Jojotheamazing/esp32-console/SdCard/Assets/UIImages/MainMenu/control.bmp

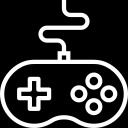
SdCard/Assets/UIImages/MainMenu/control.bmp
