Jojotheamazing/esp32-console/SdCard/Assets/UIImages/MainMenu/games.bmp

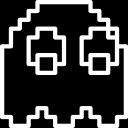
SdCard/Assets/UIImages/MainMenu/games.bmp
