Jojotheamazing/esp32-console/SdCard/music/DummyPlaylist2/cover.jpg

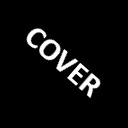
SdCard/music/DummyPlaylist2/cover.jpg
