Jojotheamazing/esp32-console/CAD/SecondaryColor/CompleteShell - ValinorStar1.step

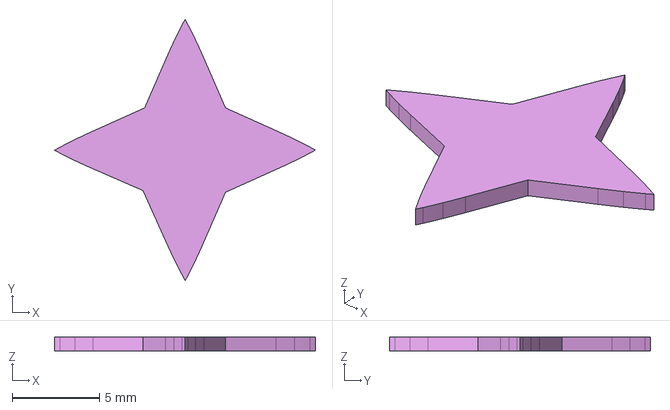
[picture p24: CAD file, 2026-09-23]
CAD/SecondaryColor/CompleteShell - ValinorStar1.step
14.9 x 15.0 x 0.8 mm
