Jojotheamazing/esp32-console/CAD/SecondaryColor/CompleteShell - BatteryCoverR.step

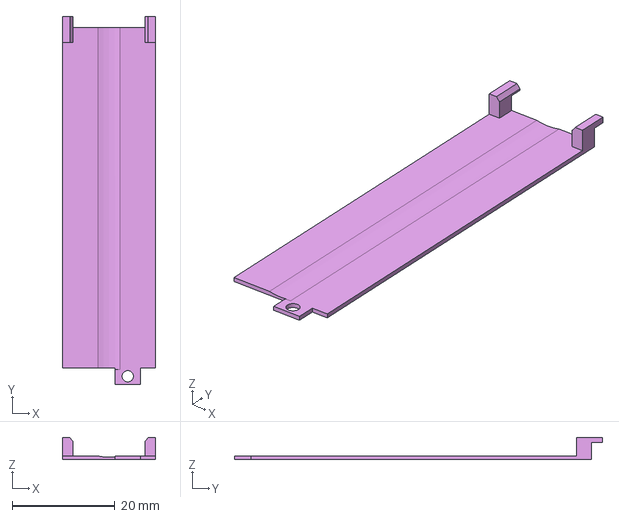
[picture p25: CAD file, 2026-09-23]
CAD/SecondaryColor/CompleteShell - BatteryCoverR.step
18.1 x 71.7 x 4.30 mm
