Jojotheamazing/esp32-console/CAD/SecondaryColor/CompleteShell - HackclubFlag.step

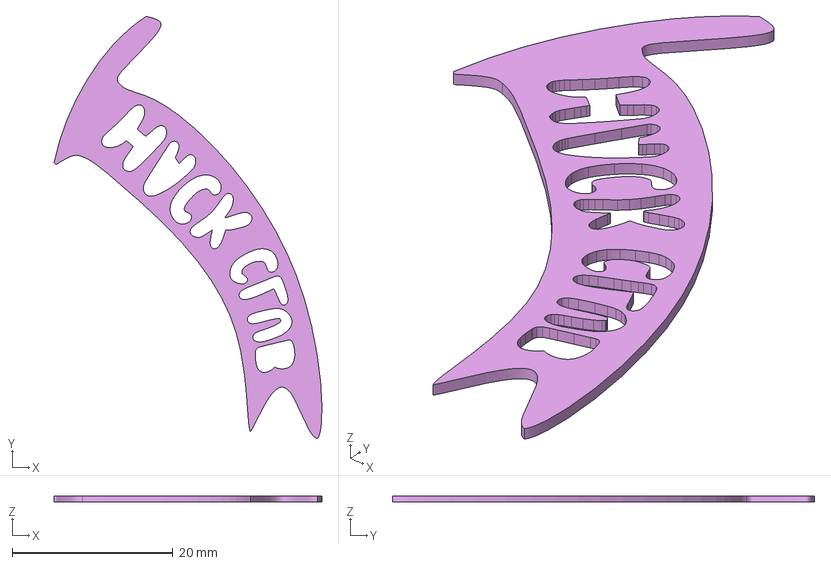
[picture p26: CAD file, 2026-09-23]
CAD/SecondaryColor/CompleteShell - HackclubFlag.step
33.4 x 52.6 x 0.8 mm
