Jojotheamazing/esp32-console/CAD/SecondaryColor/CompleteShell - ValinorStar3.step

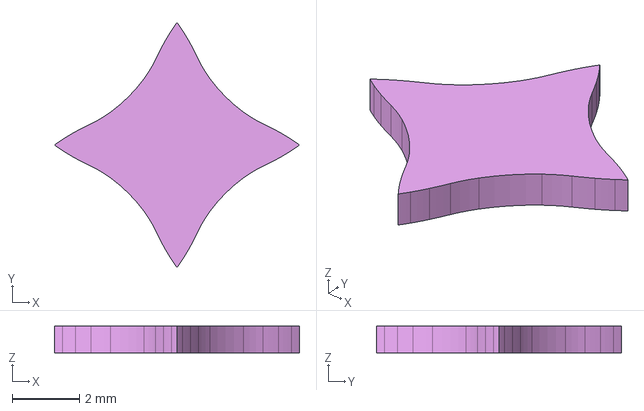
[picture p27: CAD file, 2026-09-23]
CAD/SecondaryColor/CompleteShell - ValinorStar3.step
7.31 x 7.31 x 0.8 mm
