Jojotheamazing/esp32-console/CAD/SecondaryColor/CompleteShell - GitLogo.step

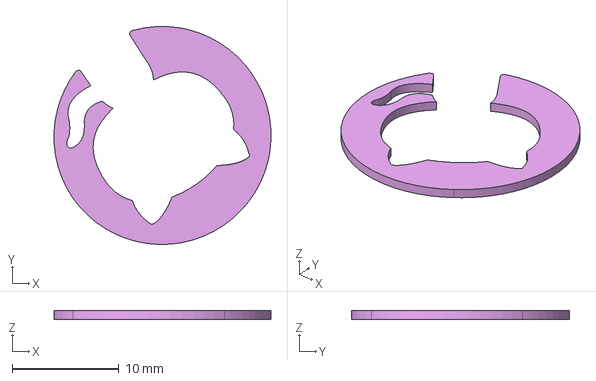
[picture p28: CAD file, 2026-09-23]
CAD/SecondaryColor/CompleteShell - GitLogo.step
20.3 x 20.4 x 0.8 mm
