Jojotheamazing/esp32-console/CAD/SecondaryColor/CompleteShell - ForgeLogo.step

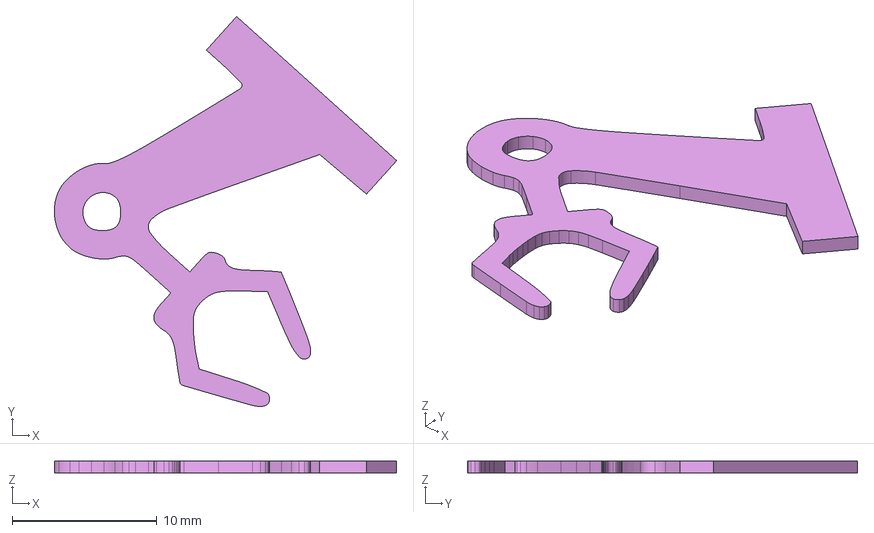
[picture p29: CAD file, 2026-09-23]
CAD/SecondaryColor/CompleteShell - ForgeLogo.step
23.6 x 26.9 x 0.8 mm
