Jojotheamazing/esp32-console/CAD/SecondaryColor/CompleteShell - ForgeO1.step

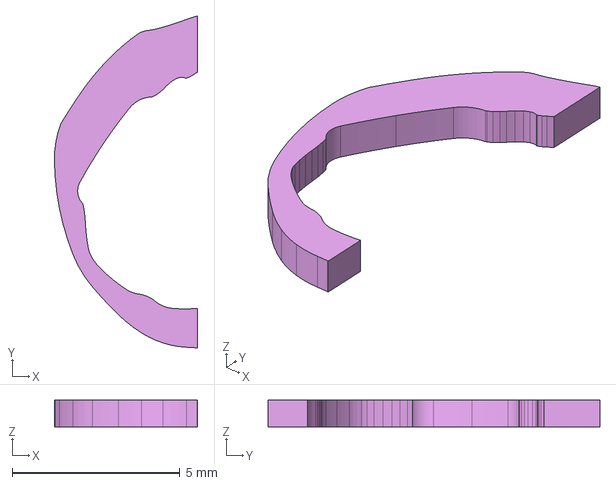
[picture p30: CAD file, 2026-09-23]
CAD/SecondaryColor/CompleteShell - ForgeO1.step
4.26 x 9.88 x 0.8 mm
