Jojotheamazing/esp32-console/CAD/MainColor/S_BUTTONS - Part 15.step

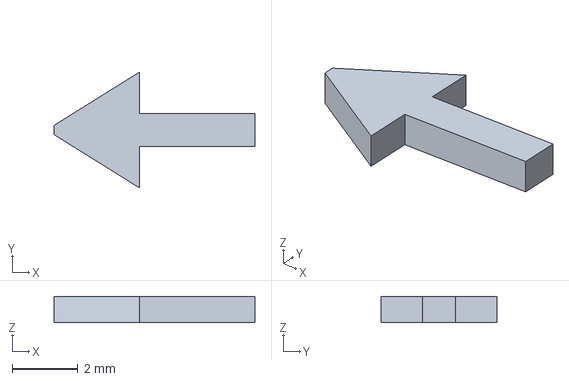
[picture p31: CAD file, 2026-09-23]
CAD/MainColor/S_BUTTONS - Part 15.step
6.10 x 3.52 x 0.8 mm
