Jojotheamazing/esp32-console/CAD/SecondaryColor/M_BUTTONS - StartButton.step

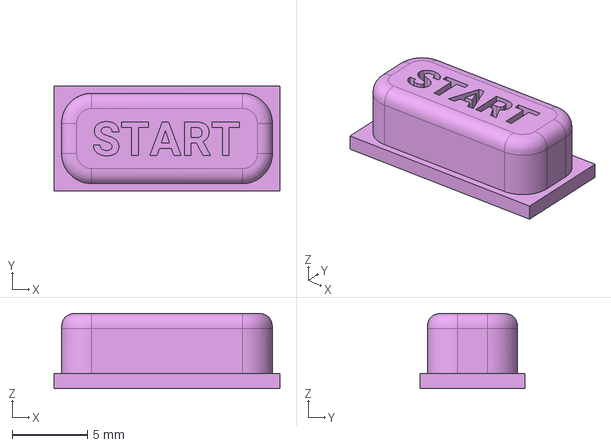
[picture p32: CAD file, 2026-09-23]
CAD/SecondaryColor/M_BUTTONS - StartButton.step
15.0 x 7.00 x 5.00 mm
