Jojotheamazing/esp32-console/CAD/MainColor/S_BUTTONS - Part 9.step

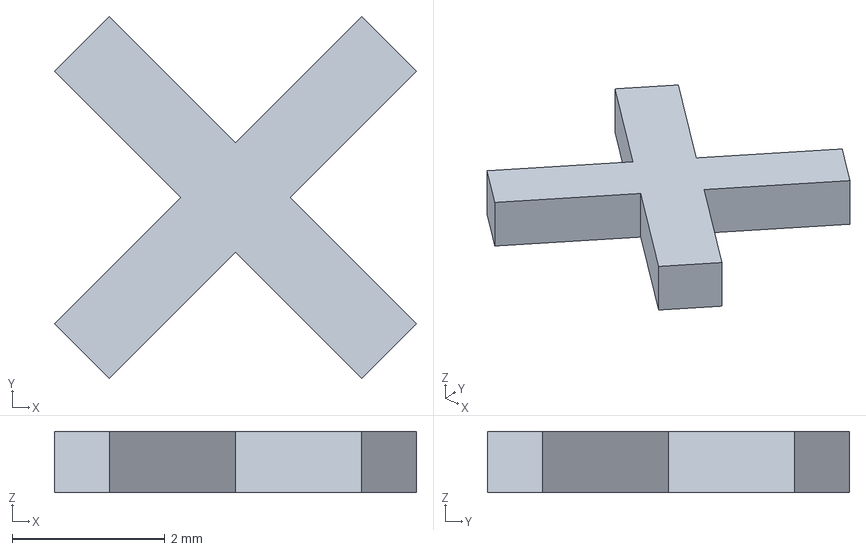
[picture p33: CAD file, 2026-09-23]
CAD/MainColor/S_BUTTONS - Part 9.step
4.74 x 4.74 x 0.8 mm
