Jojotheamazing/esp32-console/CAD/SecondaryColor/S_TOP - Volume.step

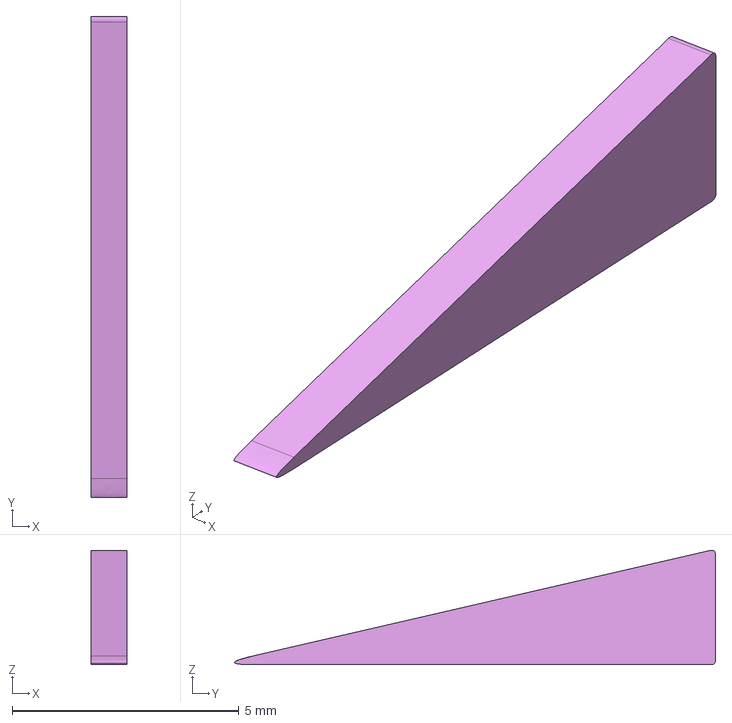
[picture p34: CAD file, 2026-09-23]
CAD/SecondaryColor/S_TOP - Volume.step
0.8 x 10.6 x 2.53 mm
