Jojotheamazing/esp32-console/CAD/SecondaryColor/M_BUTTONS - PowerButton.step

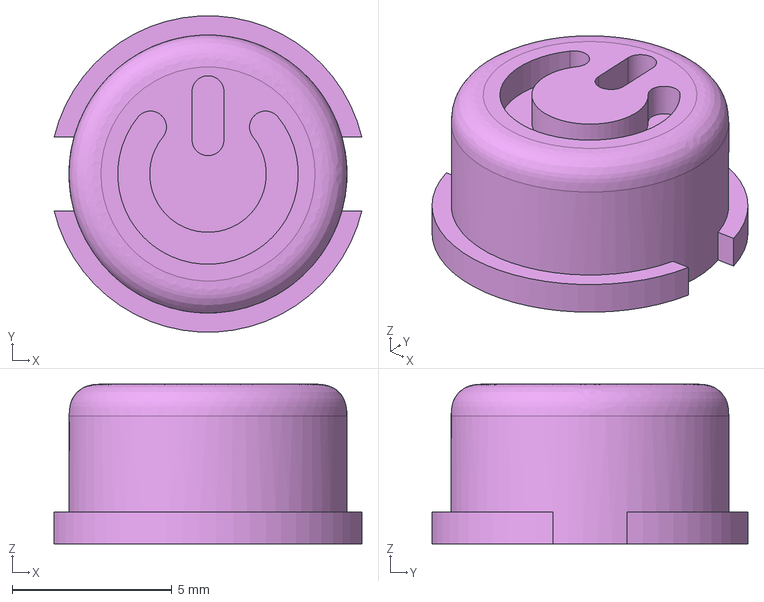
[picture p35: CAD file, 2026-09-23]
CAD/SecondaryColor/M_BUTTONS - PowerButton.step
9.63 x 9.89 x 5.00 mm
