Jojotheamazing/esp32-console/CAD/MainColor/S_BUTTONS - Part 11.step

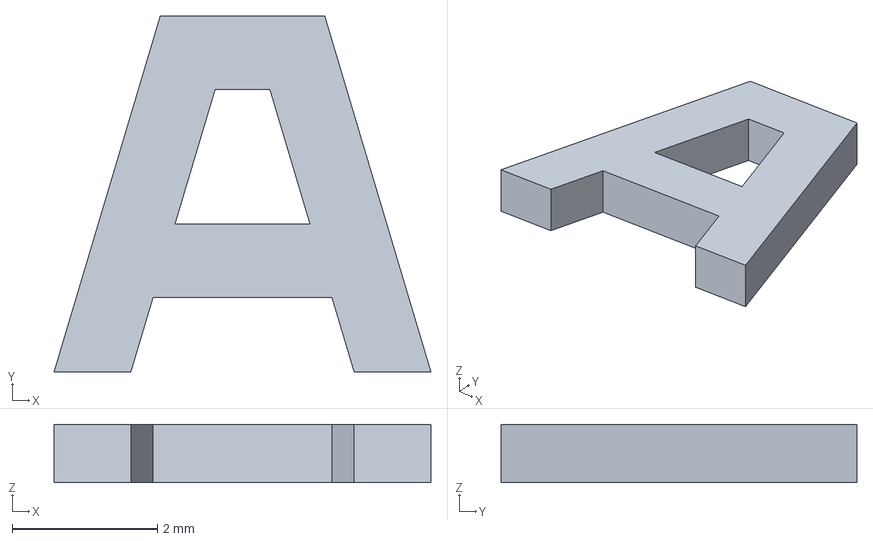
[picture p36: CAD file, 2026-09-23]
CAD/MainColor/S_BUTTONS - Part 11.step
5.19 x 4.90 x 0.8 mm
