Jojotheamazing/esp32-console/CAD/SecondaryColor/M_TOP - Part 2.step

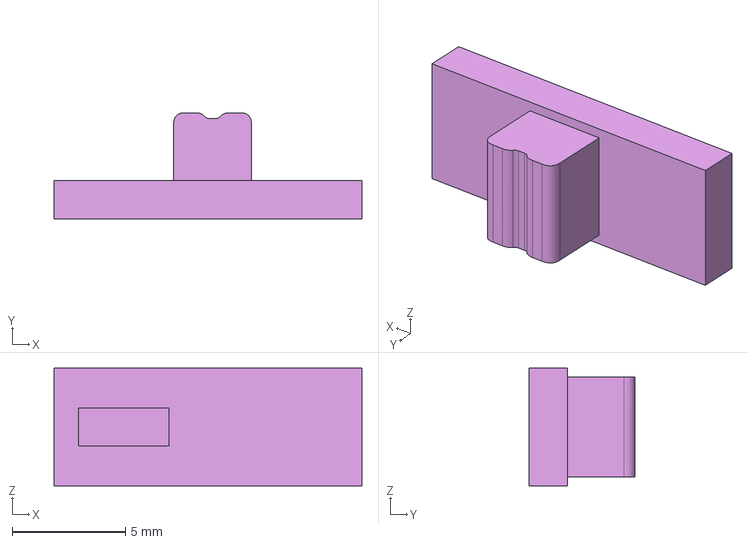
[picture p37: CAD file, 2026-09-23]
CAD/SecondaryColor/M_TOP - Part 2.step
13.6 x 4.70 x 5.20 mm
