Jojotheamazing/esp32-console/CAD/SecondaryColor/Part Studio 1 - JoystickHandle.step

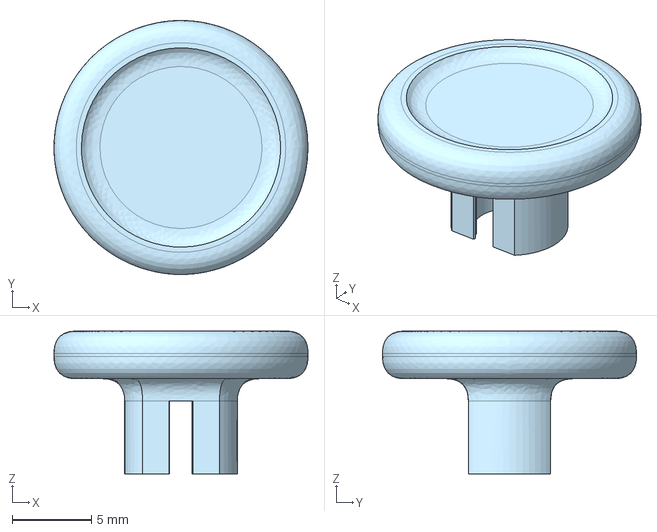
[picture p38: CAD file, 2026-09-23]
CAD/SecondaryColor/Part Studio 1 - JoystickHandle.step
16.0 x 16.0 x 9.00 mm
