Jojotheamazing/esp32-console/CAD/SecondaryColor/SecondaryColor3dDesgin.3mf

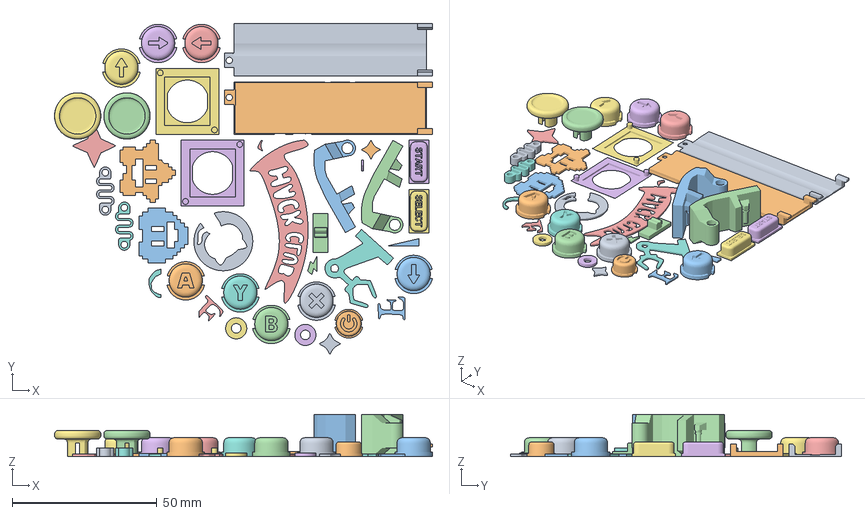
[picture p39: CAD file, 2026-09-23]
CAD/SecondaryColor/SecondaryColor3dDesgin.3mf
130.4 x 114.1 x 14.5 mm
CompleteShell - BatteryCoverR.step
CompleteShell - BatteryCoverL.step
RearButton - RearLButton.step
RearButton - RearRButton.step
CompleteShell - HackclubFlag.step
S_TOP - JoystickDecorL.step
S_TOP - JoystickDecorR.step
CompleteShell - ForgeLogo.step
CompleteShell - GitLogo.step
S_TOP - Star.step
S_TOP - Heart.step
Part Studio 1 - JoystickHandle.step x 2
S_BUTTONS - Part 8.step
S_BUTTONS - Part 7.step
S_BUTTONS - Part 5.step
S_BUTTONS - Part 4.step
S_BUTTONS - Part 3.step
S_BUTTONS - Part 1.step
S_BUTTONS - Part 6.step
S_BUTTONS - Part 2.step
CompleteShell - ValinorStar1.step
M_BUTTONS - StartButton.step
M_BUTTONS - SelectButton.step
Spring - Part 1 copy.step
Spring - Part 1.step
M_BUTTONS - PowerButton.step
CompleteShell - ForgeF.step
M_TOP - Part 2.step
CompleteShell - ForgeE2.step
ScrewLenghtFix - Part 1.step
ScrewLenghtFix - Part 1 copy.step
CompleteShell - ForgeO1.step
CompleteShell - ValinorStar3.step
CompleteShell - ValinorStar2.step
S_TOP - Volume.step
S_TOP - Lighting.step
CompleteShell - ForgeE3.step
CompleteShell - ForgeG2.step
