Jojotheamazing/esp32-console/CAD/MainColor/S_BUTTONS - Part 16.step

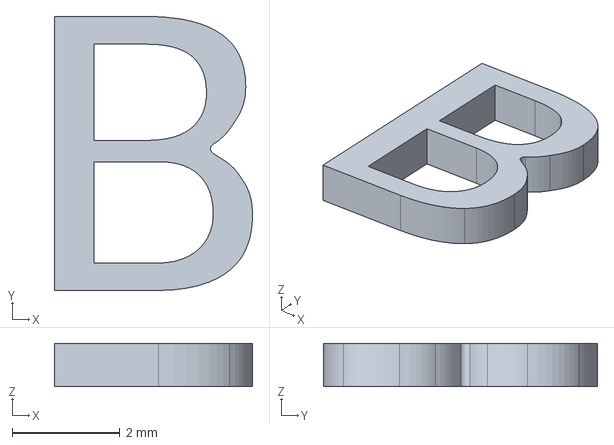
[picture p40: CAD file, 2026-09-23]
CAD/MainColor/S_BUTTONS - Part 16.step
3.67 x 5.08 x 0.8 mm
