Jojotheamazing/esp32-console/CAD/MainColor/S_BUTTONS - Part 10.step

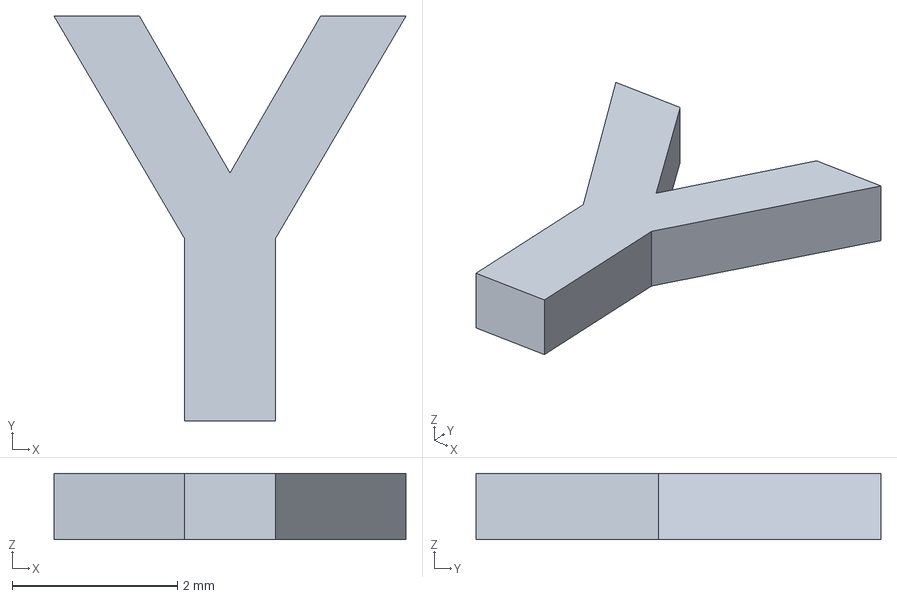
[picture p42: CAD file, 2026-09-23]
CAD/MainColor/S_BUTTONS - Part 10.step
4.26 x 4.90 x 0.8 mm
