Jojotheamazing/esp32-console/CAD/SecondaryColor/S_TOP - JoystickDecorL.step

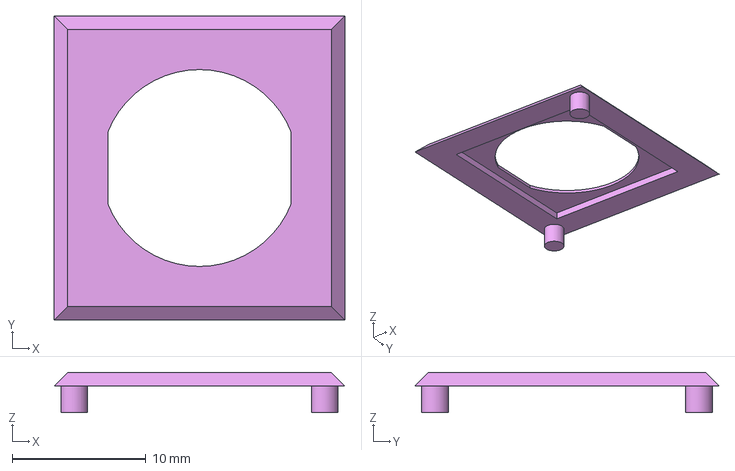
[picture p43: CAD file, 2026-09-23]
CAD/SecondaryColor/S_TOP - JoystickDecorL.step
21.7 x 22.7 x 3.00 mm
