Jojotheamazing/esp32-console/CAD/SecondaryColor/S_TOP - Heart.step

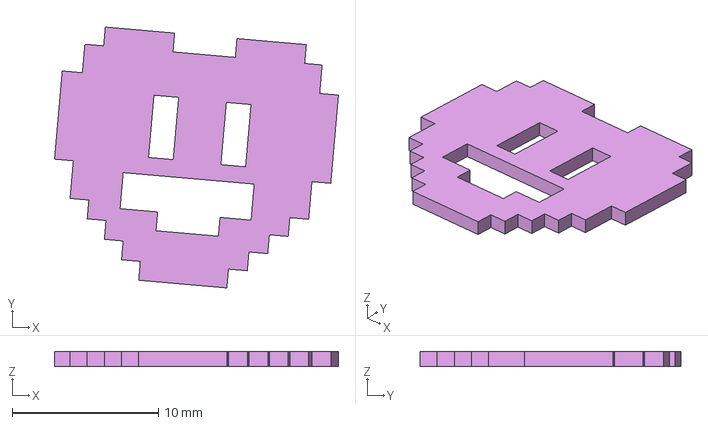
[picture p44: CAD file, 2026-09-23]
CAD/SecondaryColor/S_TOP - Heart.step
19.4 x 17.8 x 1 mm
