Jojotheamazing/esp32-console/CAD/SecondaryColor/S_TOP - Lighting.step

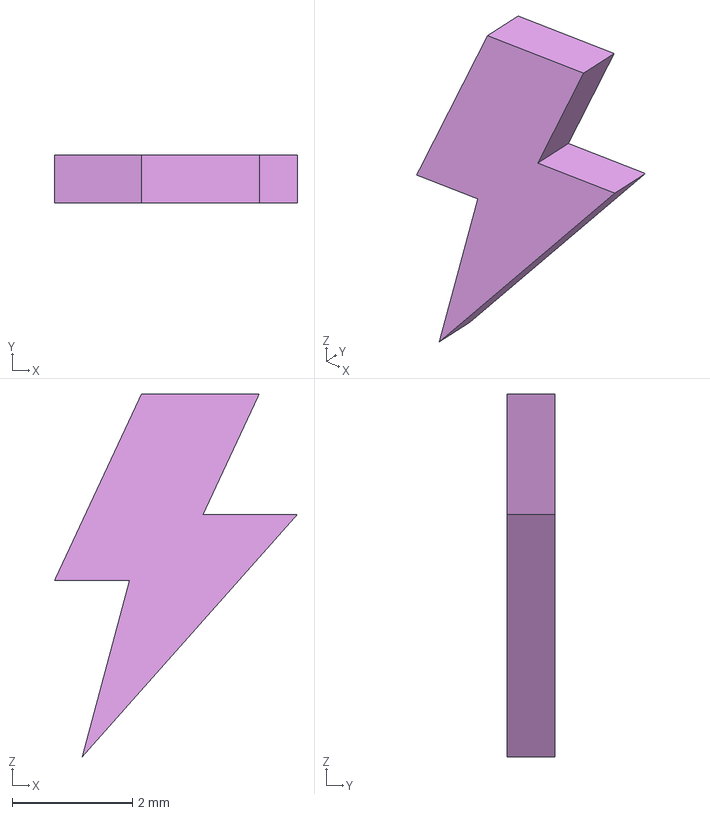
[picture p45: CAD file, 2026-09-23]
CAD/SecondaryColor/S_TOP - Lighting.step
4.04 x 0.8 x 6.03 mm
