Jojotheamazing/esp32-console/CAD/SecondaryColor/S_BUTTONS - Part 1.step

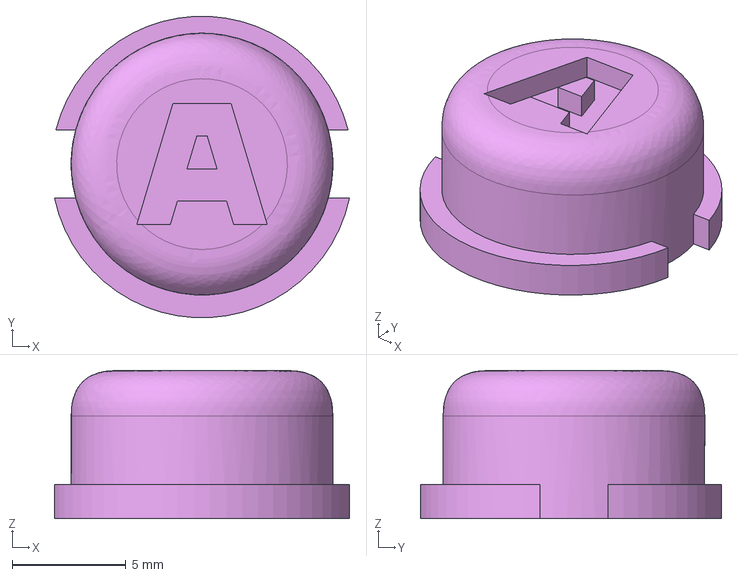
[picture p46: CAD file, 2026-09-23]
CAD/SecondaryColor/S_BUTTONS - Part 1.step
13.0 x 13.2 x 6.50 mm
