Jojotheamazing/esp32-console/CAD/SecondaryColor/RearButton - RearLButton.step

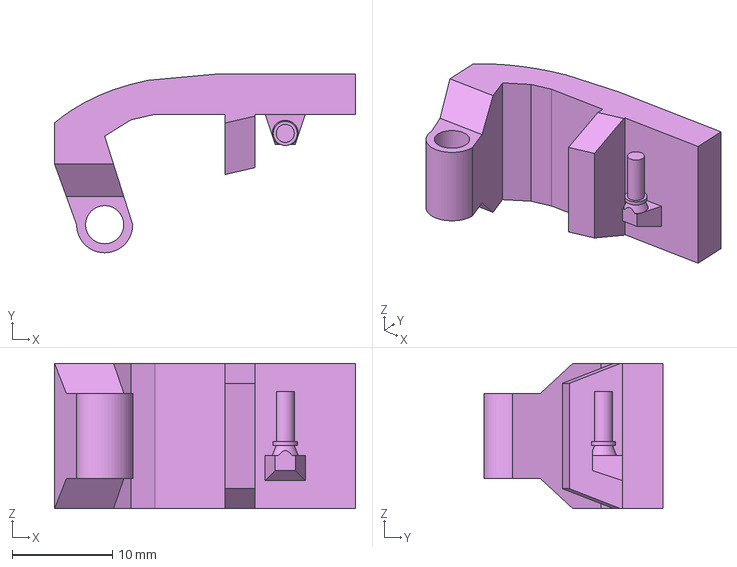
[picture p48: CAD file, 2026-09-23]
CAD/SecondaryColor/RearButton - RearLButton.step
30.0 x 17.8 x 14.5 mm
