Jojotheamazing/esp32-console/CAD/SecondaryColor/Spring - Part 1.step

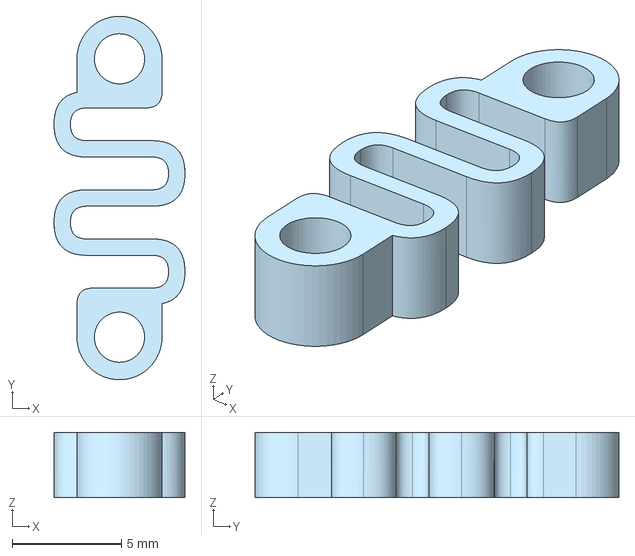
[picture p49: CAD file, 2026-09-23]
CAD/SecondaryColor/Spring - Part 1.step
6.00 x 16.6 x 3.00 mm
