Jojotheamazing/esp32-console/CAD/SecondaryColor/S_TOP - Star.step

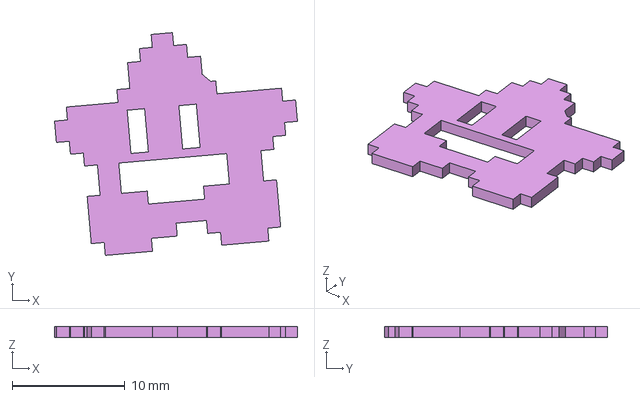
[picture p50: CAD file, 2026-09-23]
CAD/SecondaryColor/S_TOP - Star.step
21.5 x 19.7 x 1 mm
