Jojotheamazing/esp32-console/Esp32Console/Preferences.h

#pragma once
#include <TFT_eSPI.h>


#define COLOR_SELECTED 0x9994 // highlighted menu item
#define COLOR_TEXT TFT_WHITE // normal text
#define COLOR_HINT TFT_DARKGREY   // hints,subtitles
#define COLOR_ACCENT TFT_CYAN // bluetooth
#define COLOR_SUCCESS TFT_GREEN  // connected, saved ok
#define COLOR_DANGER TFT_RED // errors
#define COLOR_BG TFT_BLACK// background


#define FONT_TITLE FF23 //page titles
#define FONT_BODY FF18 //normal items
#define FONT_SMALL FF17 //hints
